tominabox1/Le-Chiffre-Keyboard/Cases/OG Case/Le Chiffre Incline Bottom P3D Mod.stl

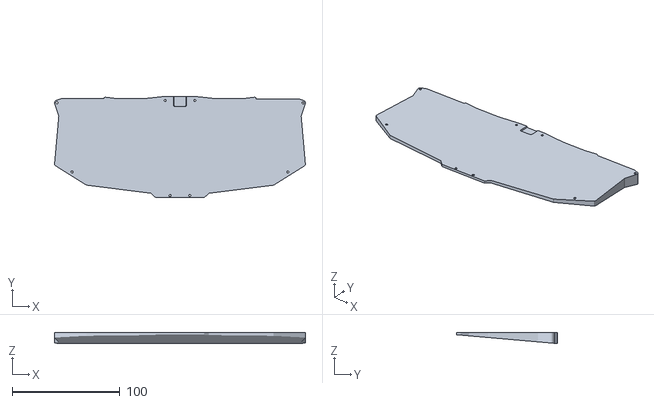
[picture p15: CAD file, 2020-05-30]
Cases/OG Case/Le Chiffre Incline Bottom P3D Mod.stl
232.7 x 94.0 x 10.3
