tominabox1/Le-Chiffre-Keyboard/Cases/OG Case/Le Chiffre v16.step

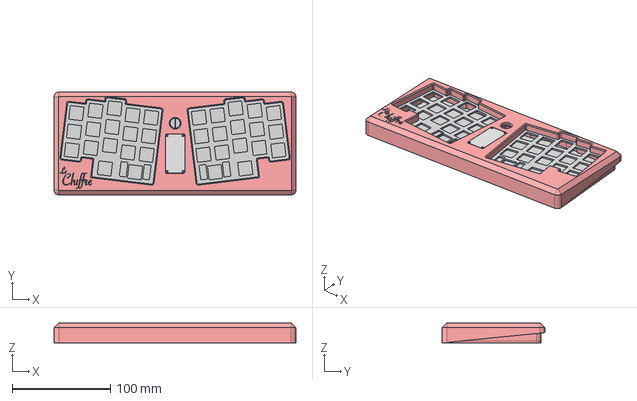
[picture p16: CAD file, 2020-05-03]
Cases/OG Case/Le Chiffre v16.step
246.5 x 104.9 x 20.1 mm
