tominabox1/Le-Chiffre-Keyboard/Cases/OG Case/Bottom Left.stl

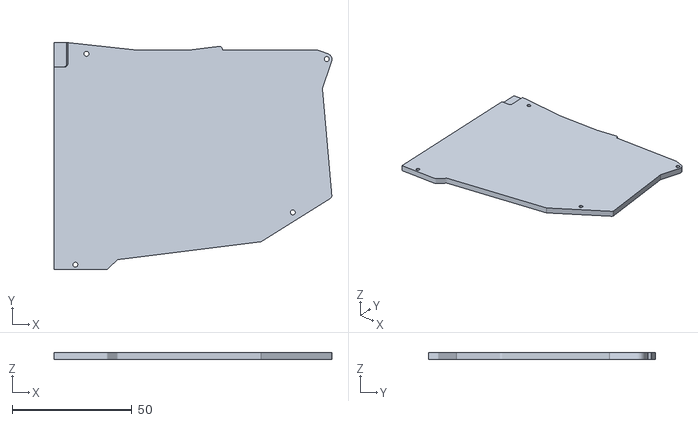
[picture p17: CAD file, 2020-05-03]
Cases/OG Case/Bottom Left.stl
116.1 x 94.8 x 3.00
